cva1003/TFG/img/ActivForce_Attachments.jpg

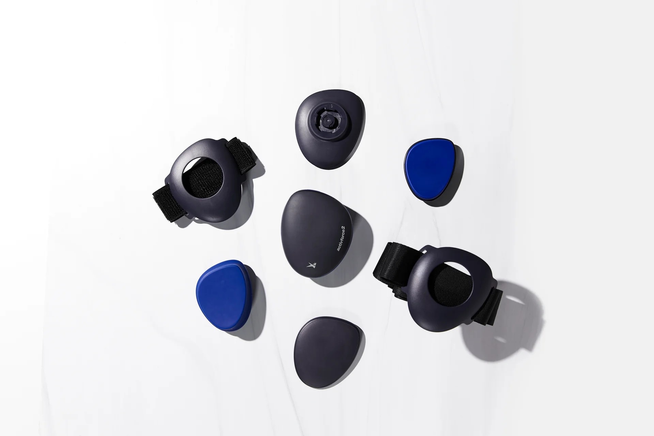
img/ActivForce_Attachments.jpg
