cva1003/TFG/img/cable usb.png

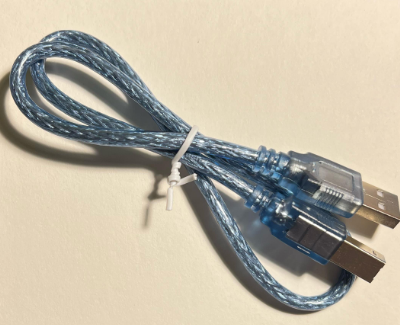
img/cable usb.png
