cva1003/TFG/img/cable_dupont.png

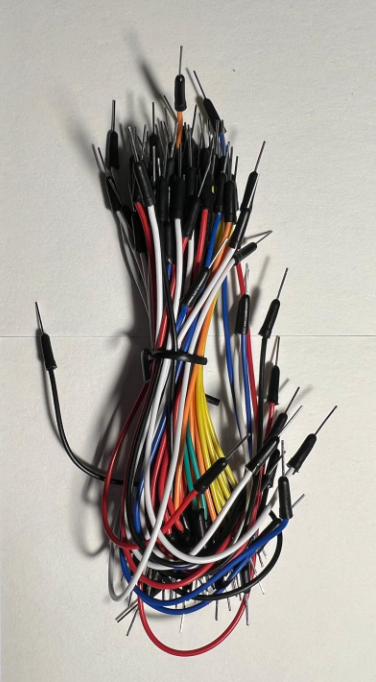
img/cable_dupont.png
