cva1003/TFG/img/CodigoArduino1.png

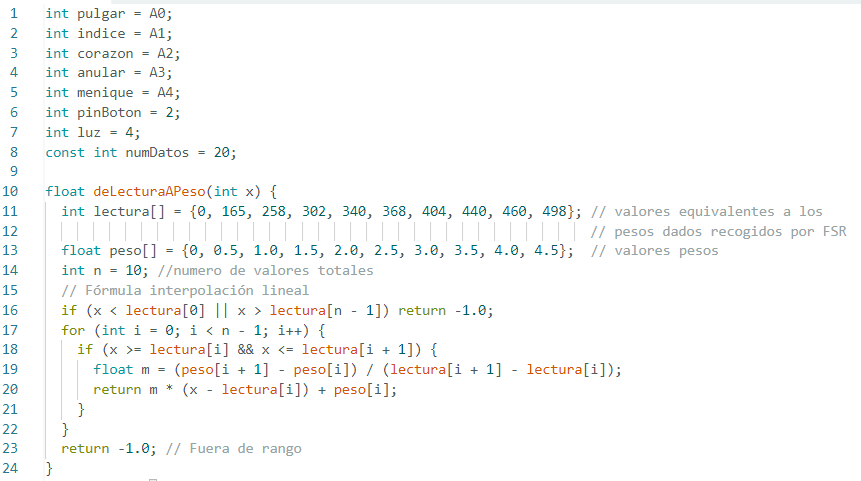
img/CodigoArduino1.png
