cva1003/TFG/img/CodigoArduino2.png

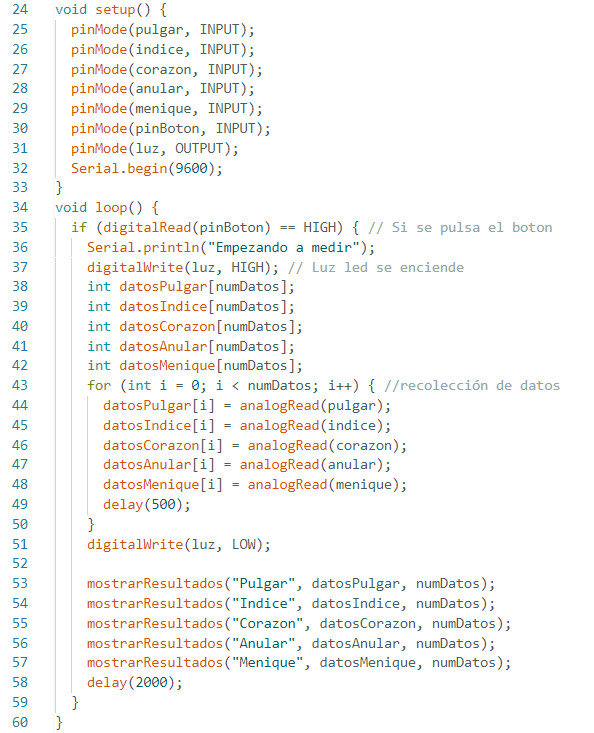
img/CodigoArduino2.png
