cva1003/TFG/img/CodigoArduino3.png

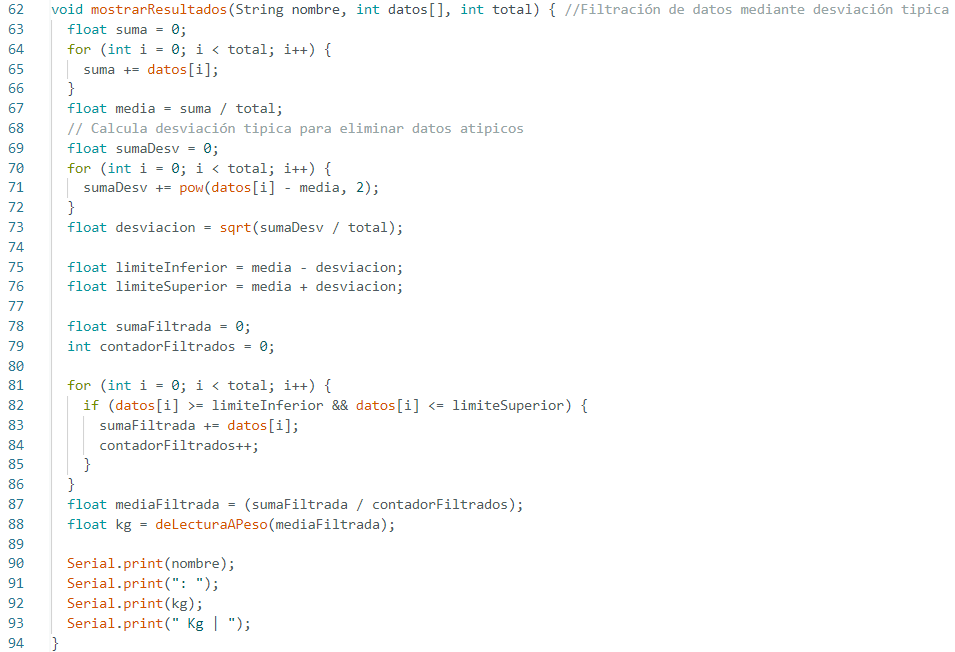
img/CodigoArduino3.png
