cva1003/TFG/img/Datos.png

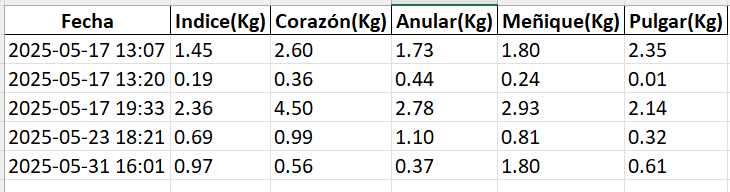
img/Datos.png
