cva1003/TFG/img/Datos_medidas.png

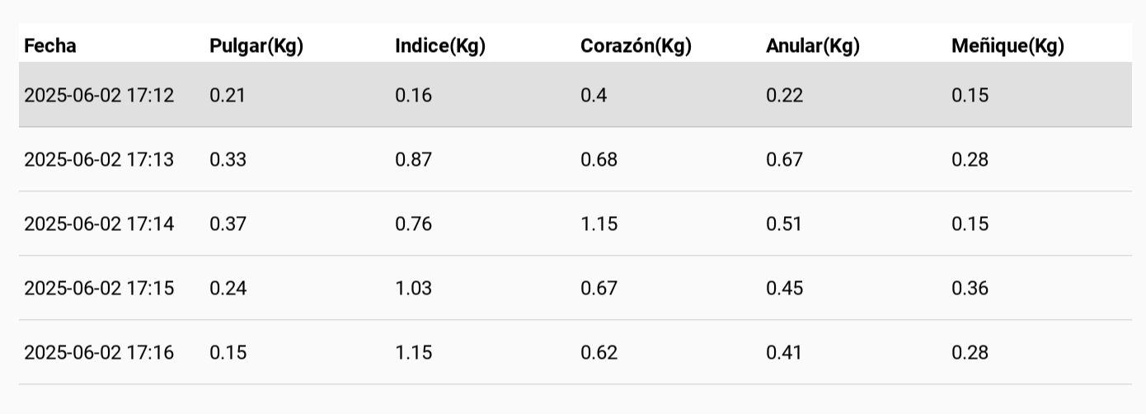
img/Datos_medidas.png
