cva1003/TFG/img/Diagrama de clases.png

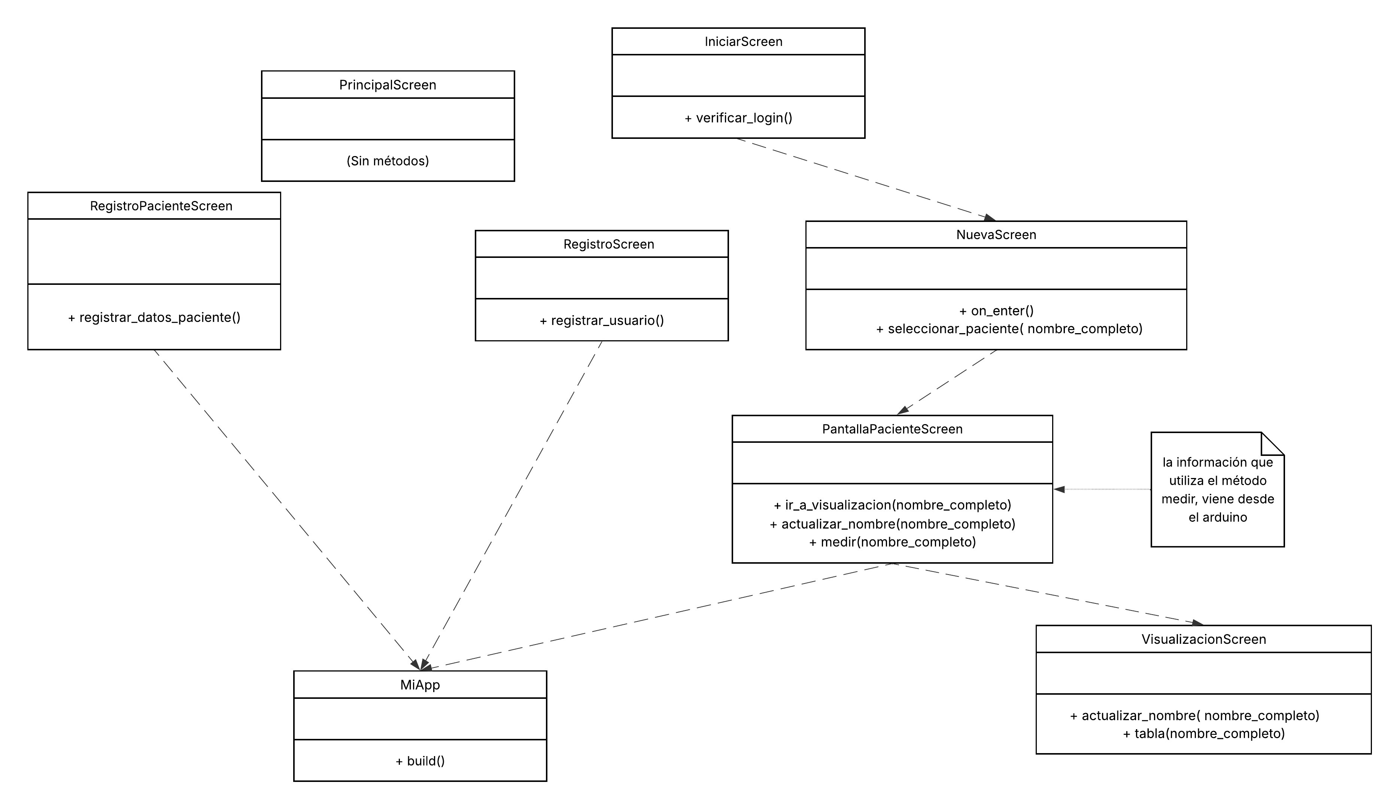
img/Diagrama de clases.png
