cva1003/TFG/img/Diagrama_flujo_arduino.png

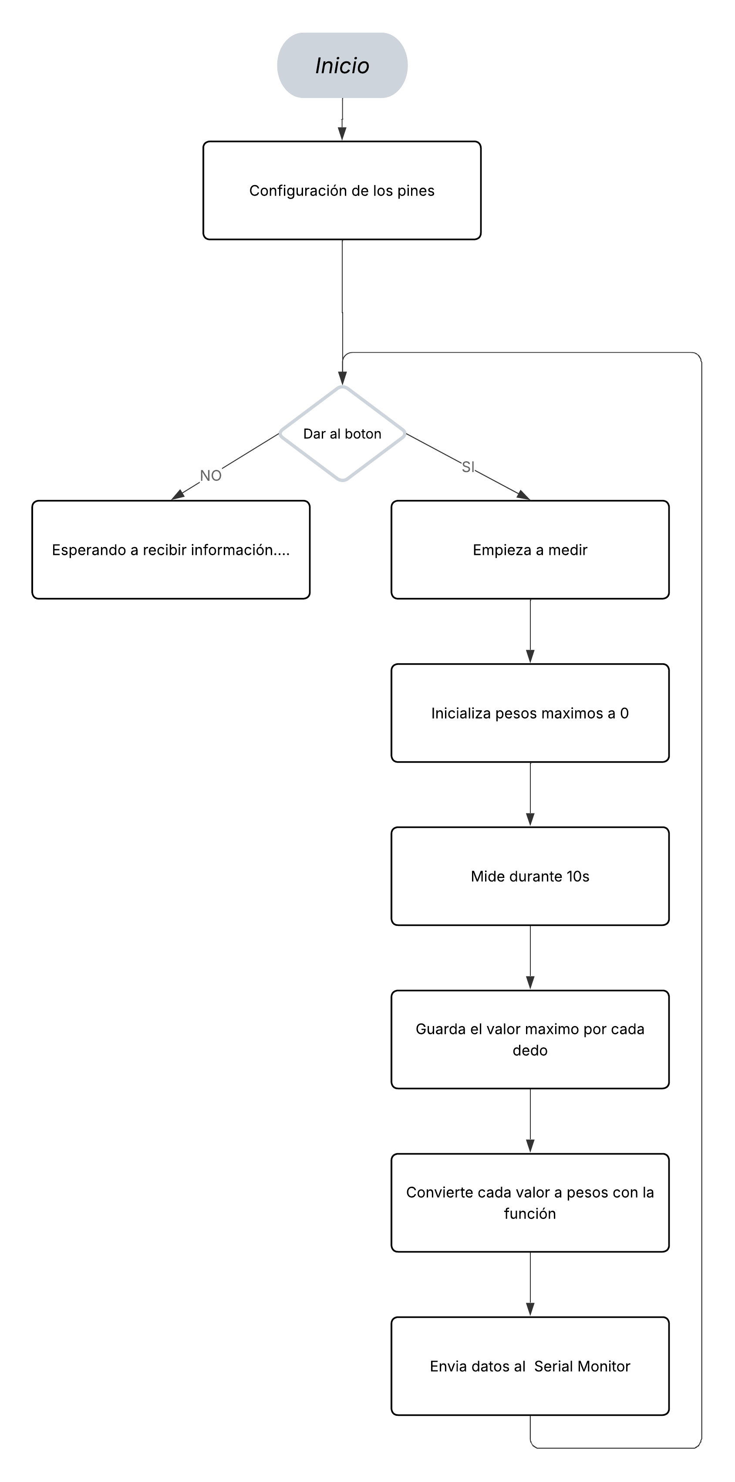
img/Diagrama_flujo_arduino.png
