cva1003/TFG/img/Dinamometro pera.jpeg

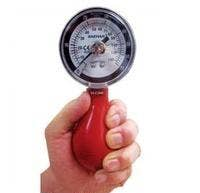
img/Dinamometro pera.jpeg
