cva1003/TFG/img/dispositivo Revista.jpg

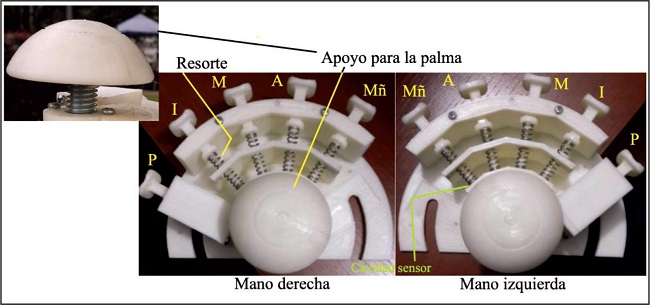
img/dispositivo Revista.jpg
