cva1003/TFG/img/Dupuytrent.png

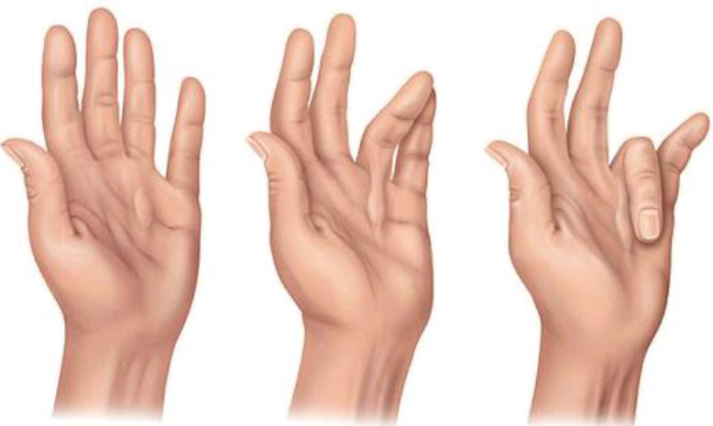
img/Dupuytrent.png
