cva1003/TFG/img/Grafica peso-valor.png

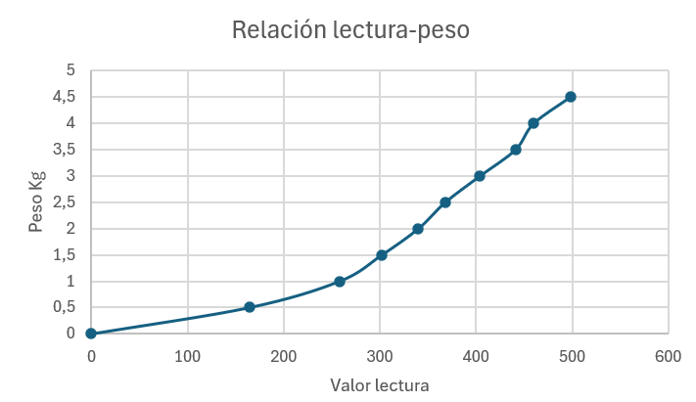
img/Grafica peso-valor.png
