cva1003/TFG/img/Huesos_mano.png

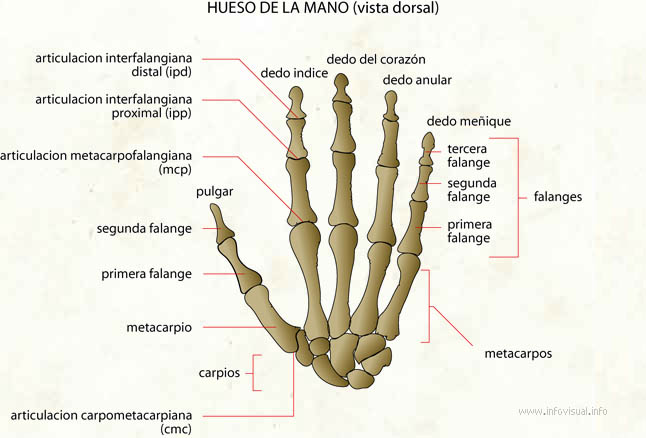
img/Huesos_mano.png
