cva1003/TFG/img/Luz_encendido.png

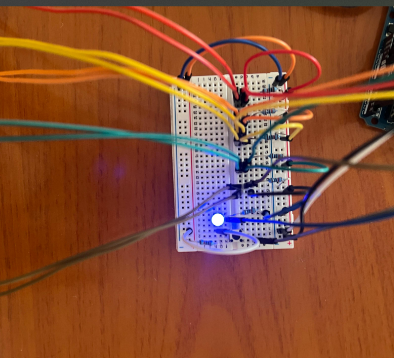
img/Luz_encendido.png
