cva1003/TFG/img/Luzled.png

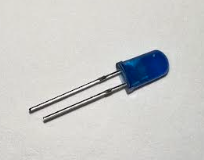
img/Luzled.png
