cva1003/TFG/img/Mango2.png

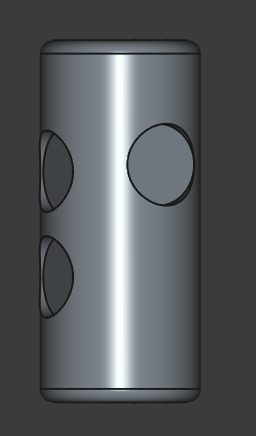
img/Mango2.png
