cva1003/TFG/img/Mango3.png

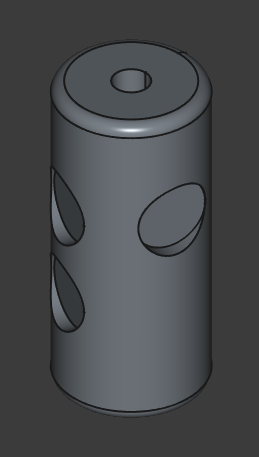
img/Mango3.png
