cva1003/TFG/img/Mano_nervios.png

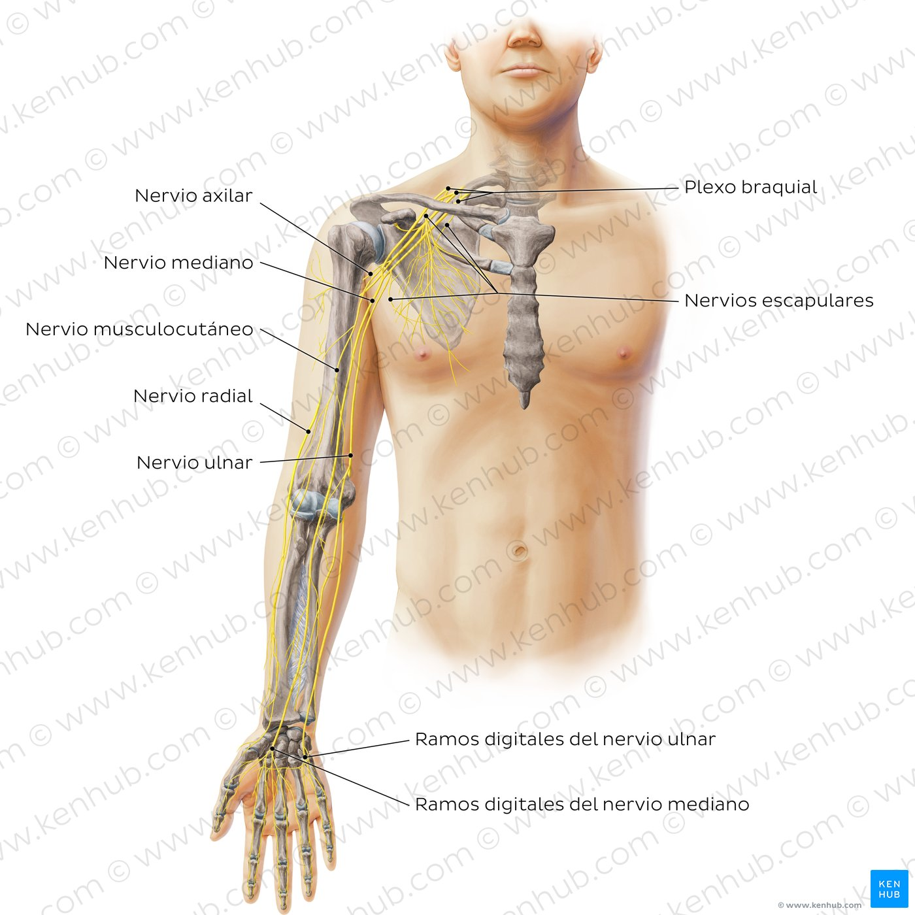
img/Mano_nervios.png
