cva1003/TFG/img/MAP-80K1S.jpg

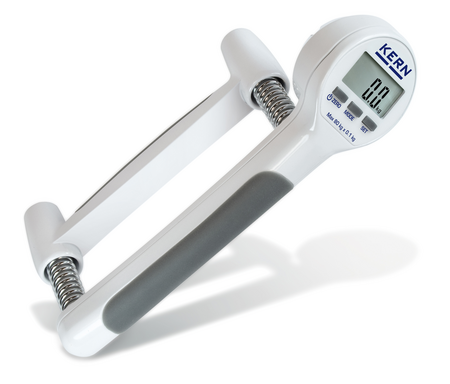
img/MAP-80K1S.jpg
