cva1003/TFG/img/MicroFET 2.jpg

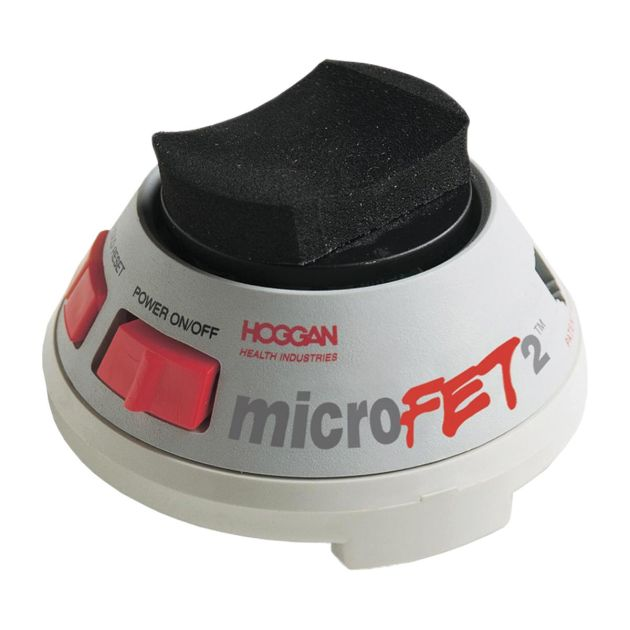
img/MicroFET 2.jpg
