cva1003/TFG/img/Musculos_mano.png

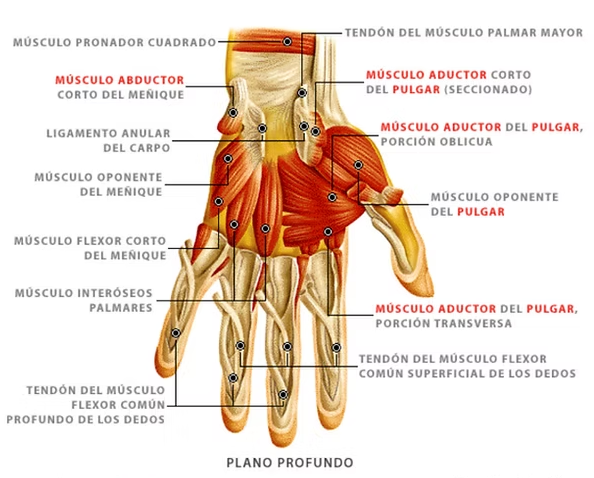
img/Musculos_mano.png
