cva1003/TFG/img/Nodulos.png

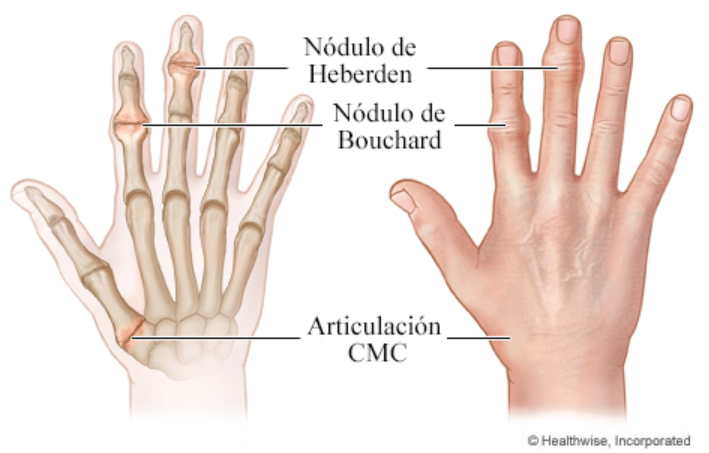
img/Nodulos.png
