cva1003/TFG/img/ODS.png

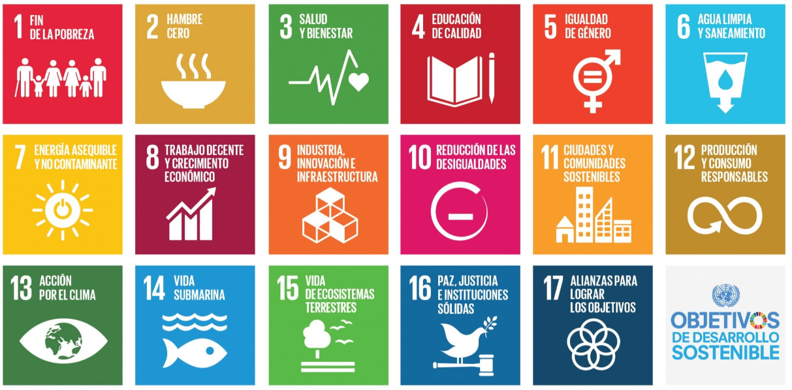
img/ODS.png
