cva1003/TFG/img/Pantalla CMD.png

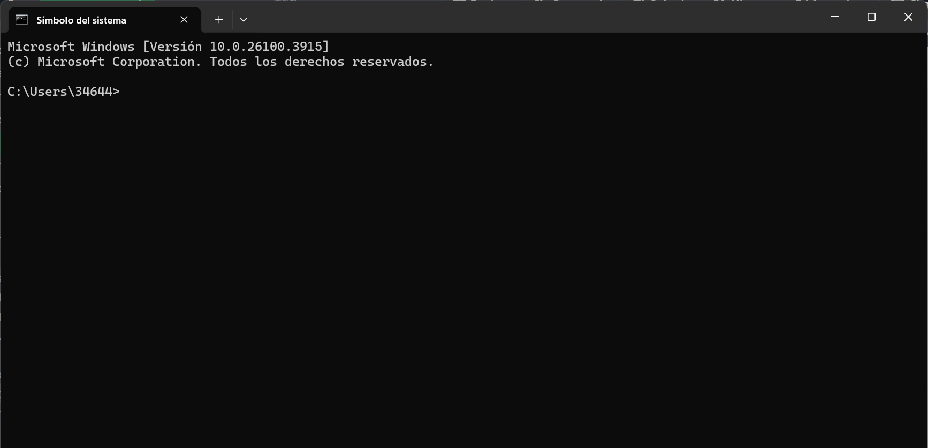
img/Pantalla CMD.png
