cva1003/TFG/img/Pantalla grafica.png

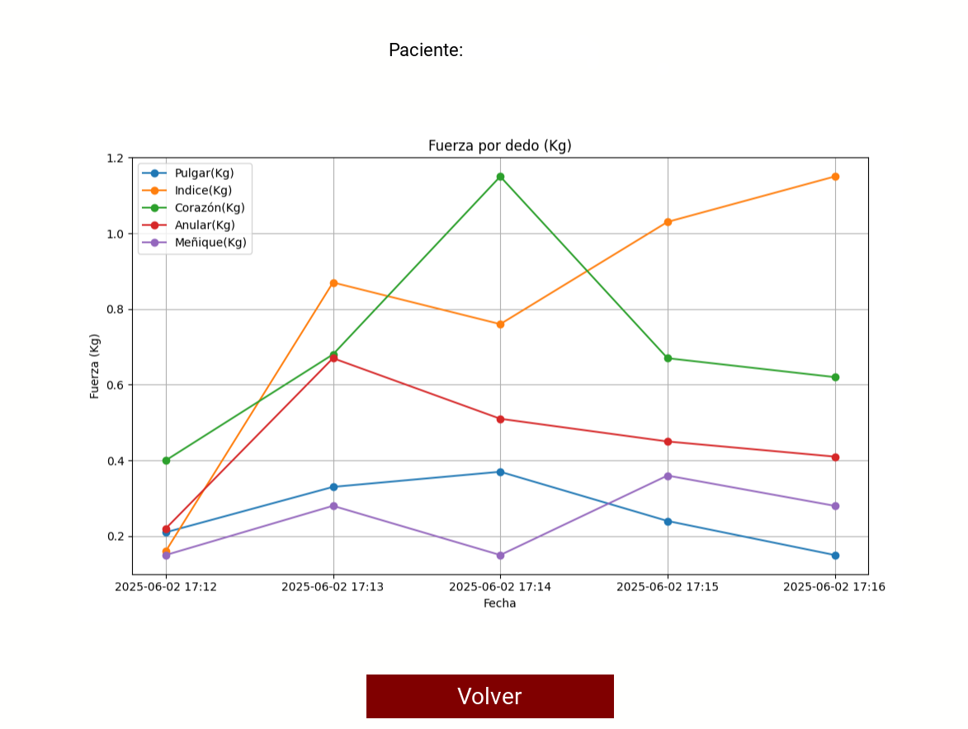
img/Pantalla grafica.png
