cva1003/TFG/img/pantalla inicio arduino IDE.png

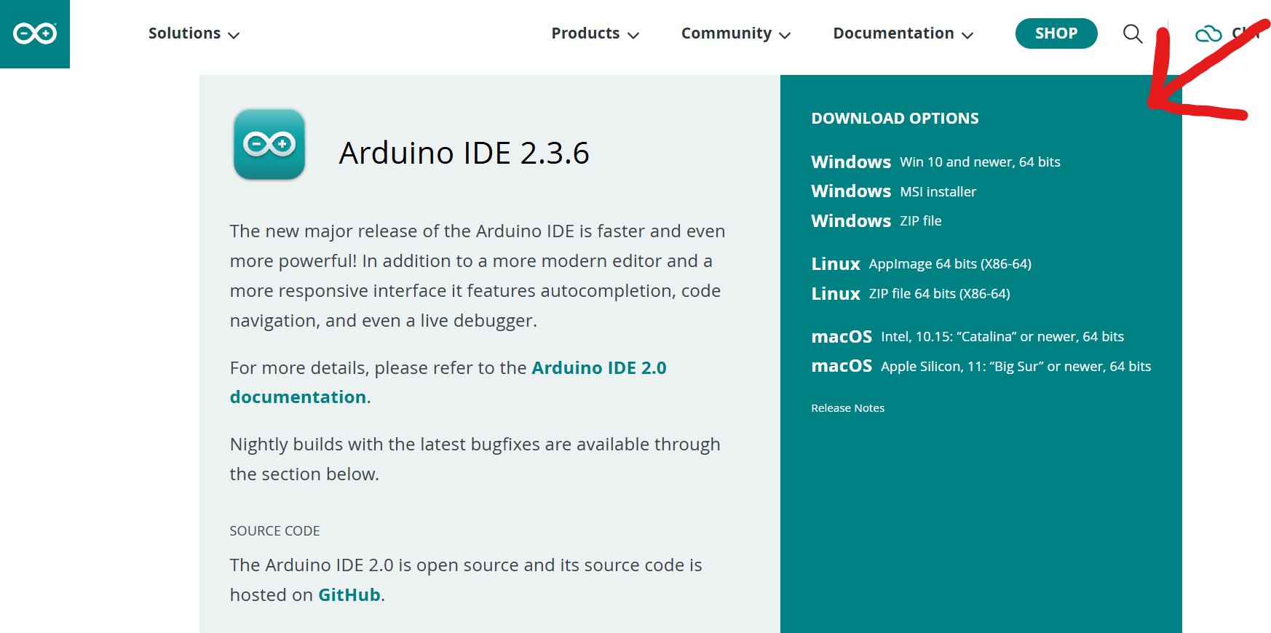
img/pantalla inicio arduino IDE.png
