cva1003/TFG/img/pantalla inicio python.png

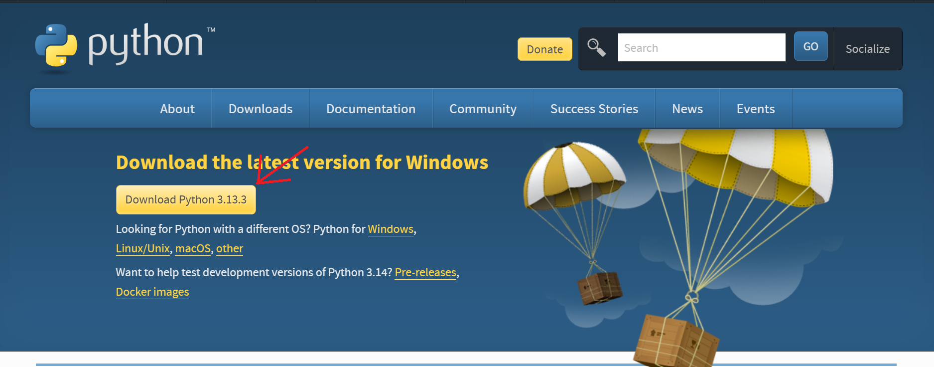
img/pantalla inicio python.png
