cva1003/TFG/img/Pantalla Inicio Sesión.png

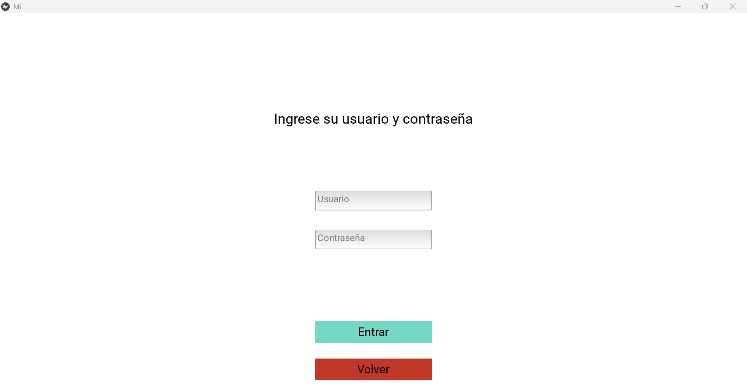
img/Pantalla Inicio Sesión.png
