cva1003/TFG/img/Pantalla Inicio.png

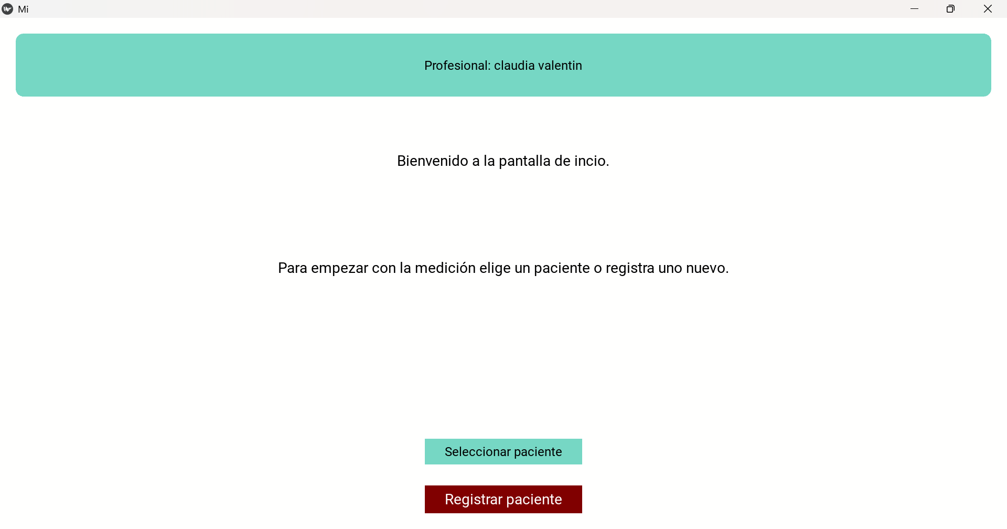
img/Pantalla Inicio.png
