cva1003/TFG/img/Pantalla paciente.png

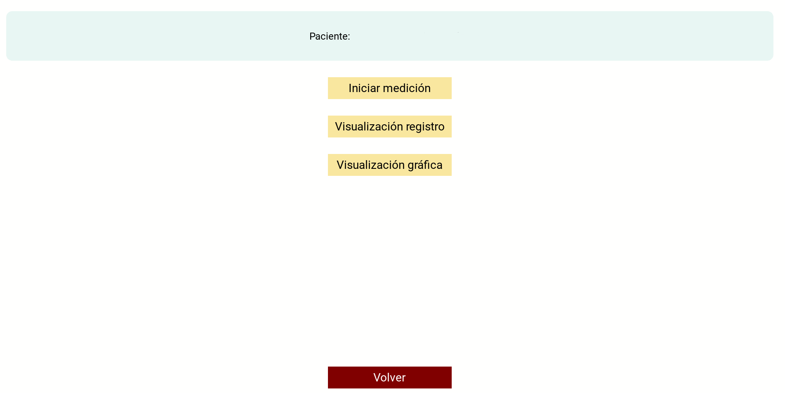
img/Pantalla paciente.png
