cva1003/TFG/img/Pantalla principal.png

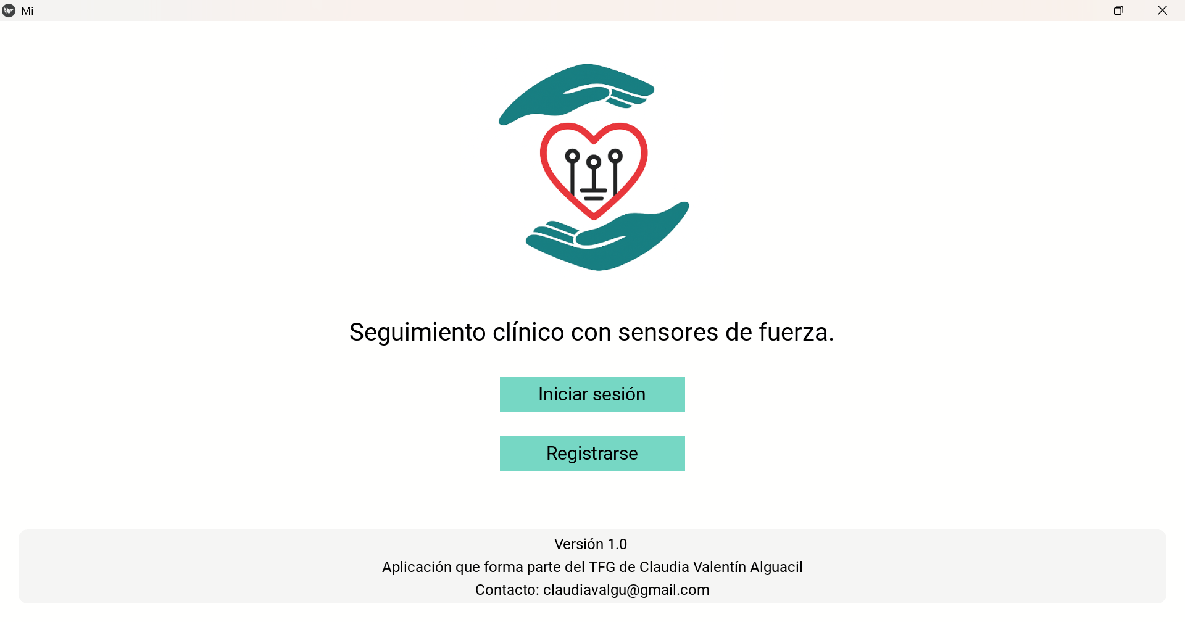
img/Pantalla principal.png
