cva1003/TFG/img/Pantalla registrar Paciente.png

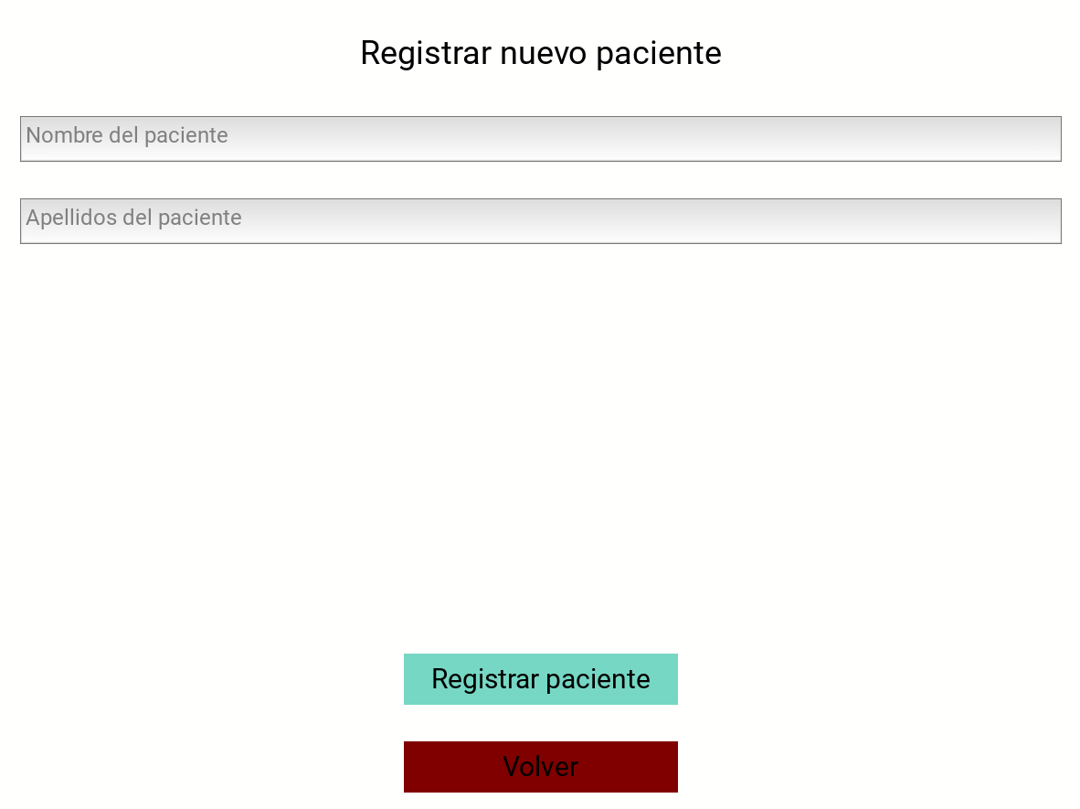
img/Pantalla registrar Paciente.png
