cva1003/TFG/img/Pantalla Registrar Usuario.png

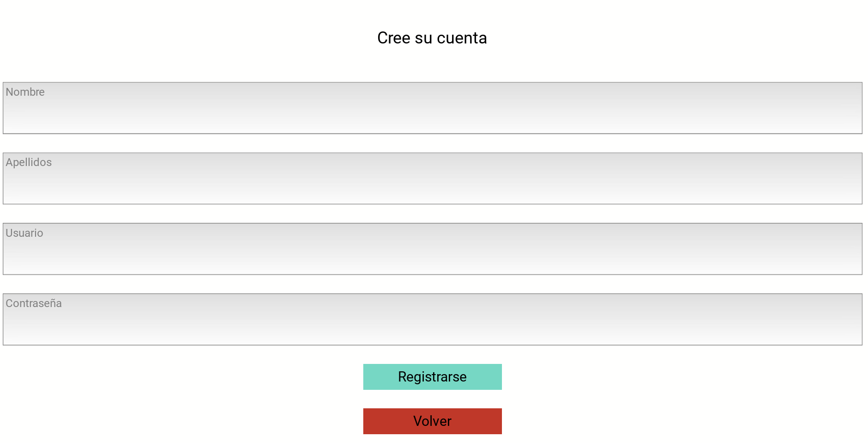
img/Pantalla Registrar Usuario.png
