cva1003/TFG/img/pinBoton.png

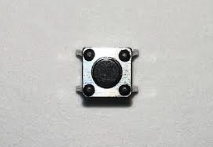
img/pinBoton.png
