cva1003/TFG/img/placa elegoo.png

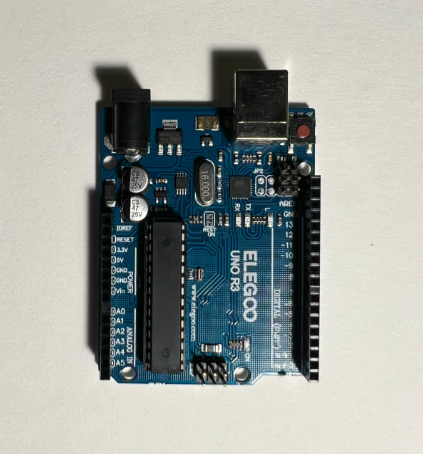
img/placa elegoo.png
