cva1003/TFG/img/planificación.png

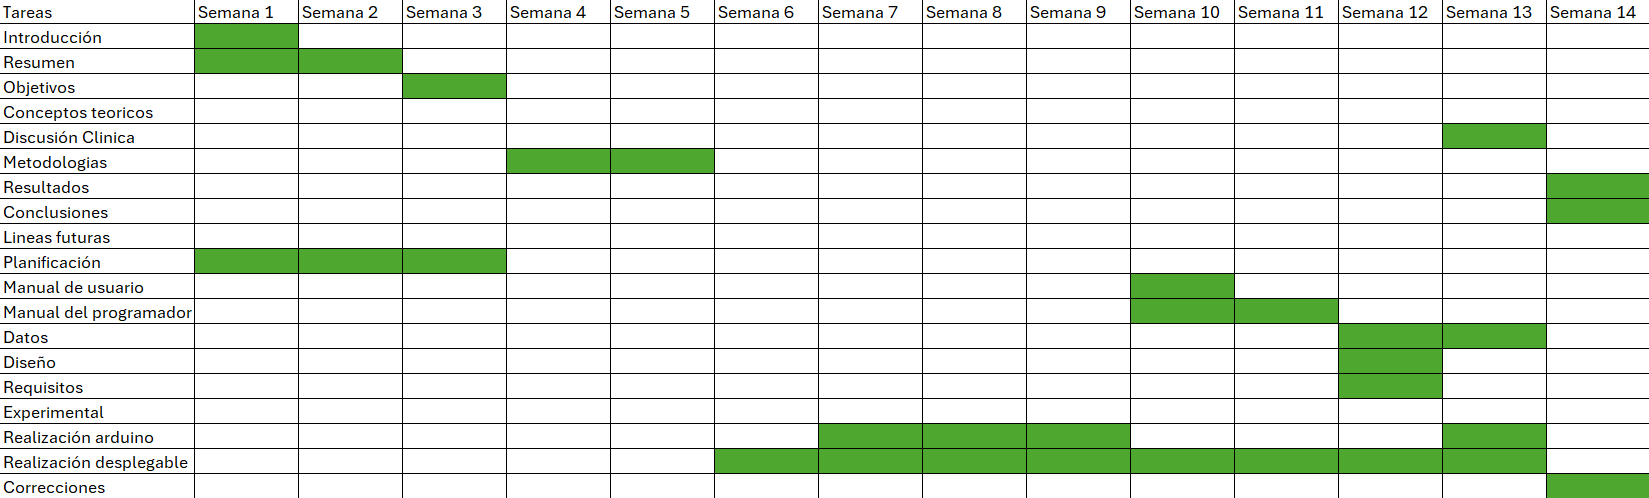
img/planificación.png
