cva1003/TFG/img/Protoboard.png

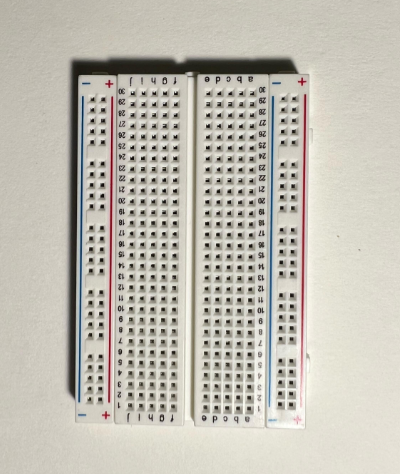
img/Protoboard.png
