cva1003/TFG/img/Prototipo_s.png

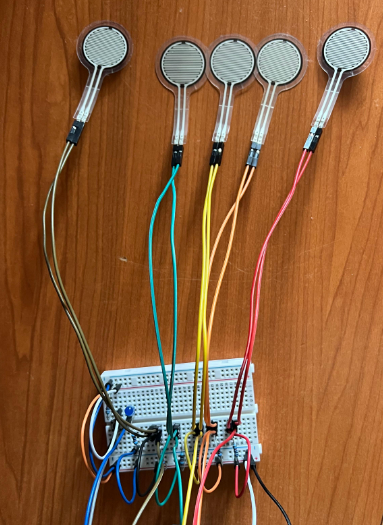
img/Prototipo_s.png
