cva1003/TFG/img/Resistencias.png

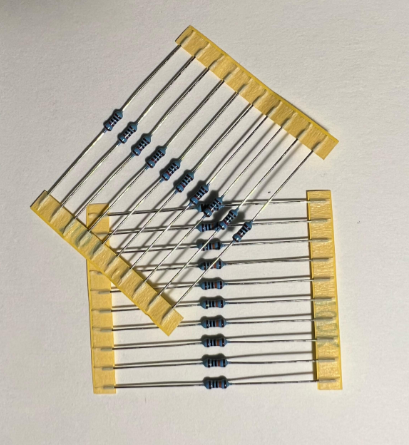
img/Resistencias.png
