cva1003/TFG/img/Rizartrosis.png

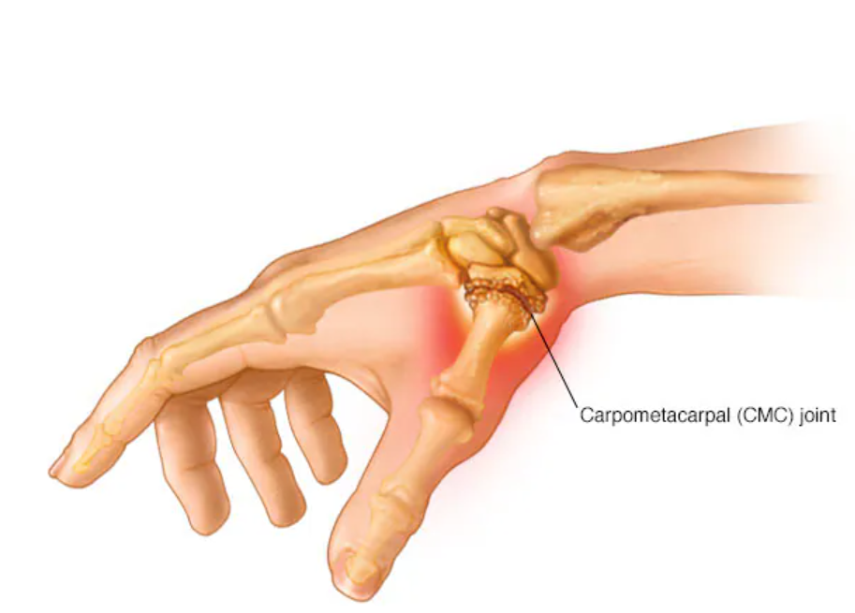
img/Rizartrosis.png
