cva1003/TFG/img/sensor.png

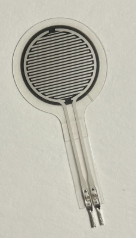
img/sensor.png
