cva1003/TFG/img/sensor_mano.png

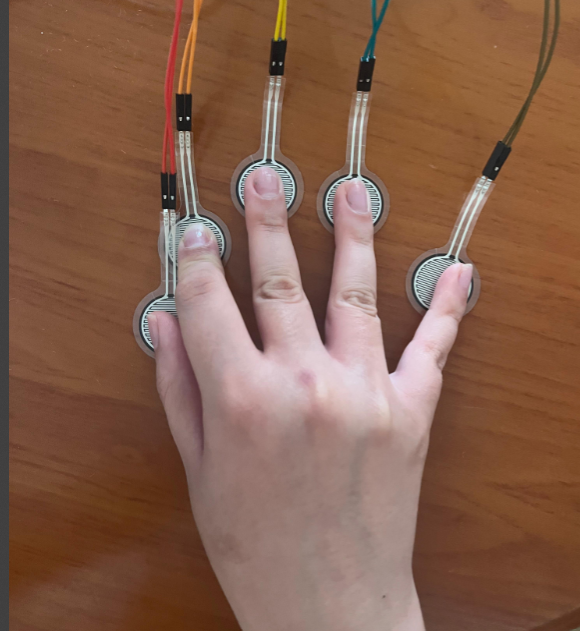
img/sensor_mano.png
