cva1003/TFG/img/Sensores.png

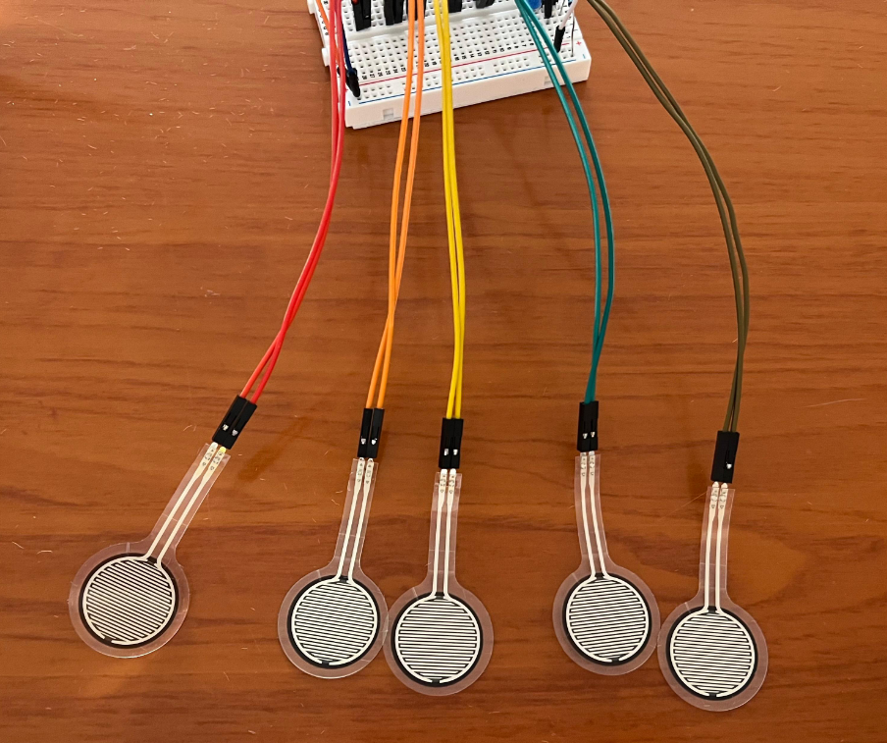
img/Sensores.png
