cva1003/TFG/img/Tabla_Canadiense.png

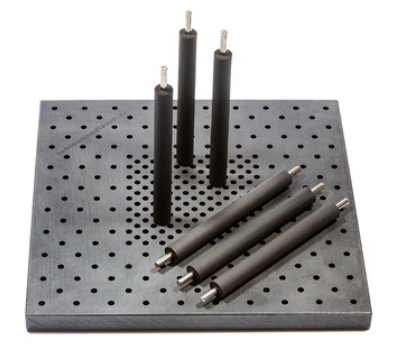
img/Tabla_Canadiense.png
