cva1003/TFG/img/TesisGuatemala.png

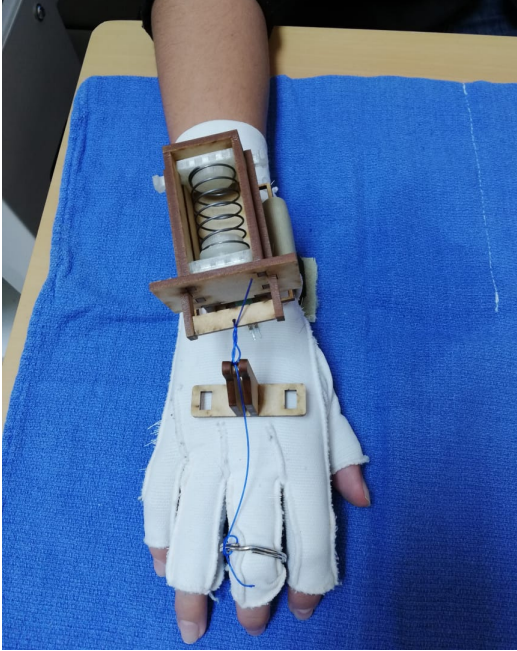
img/TesisGuatemala.png
