cva1003/TFG/img/Tunel_carpiano.png

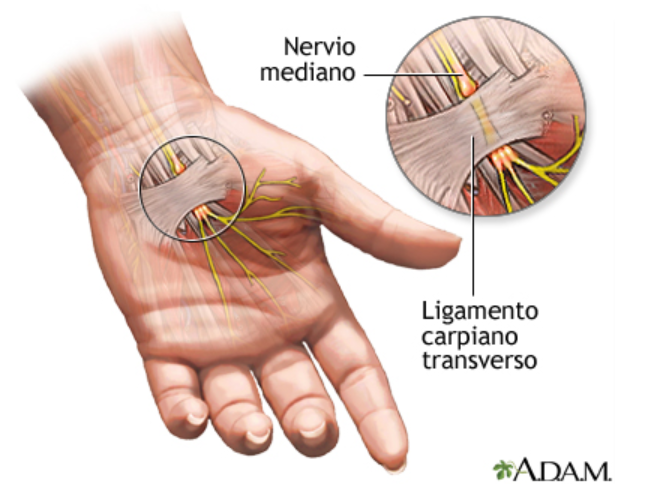
img/Tunel_carpiano.png
