cva1003/TFG/img/Vista esquematica prototipo.png

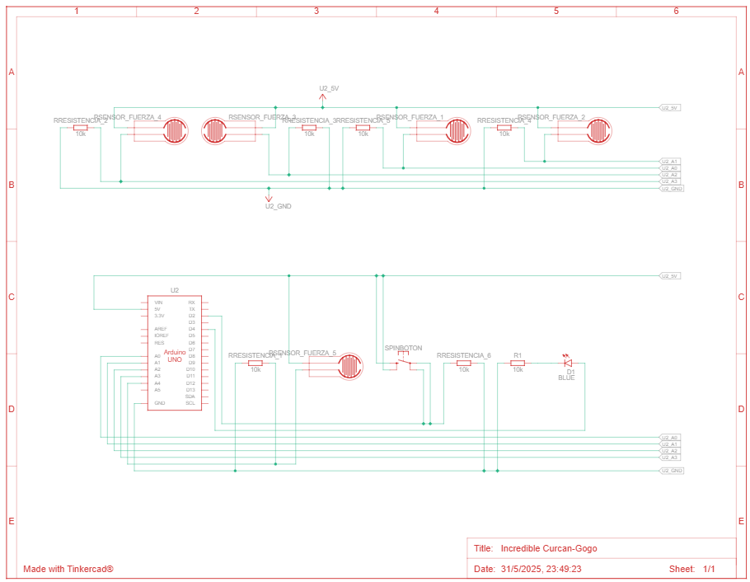
img/Vista esquematica prototipo.png
